z80/mocap_hardware/cad_drawings/hand/imu_holder_middle.stl

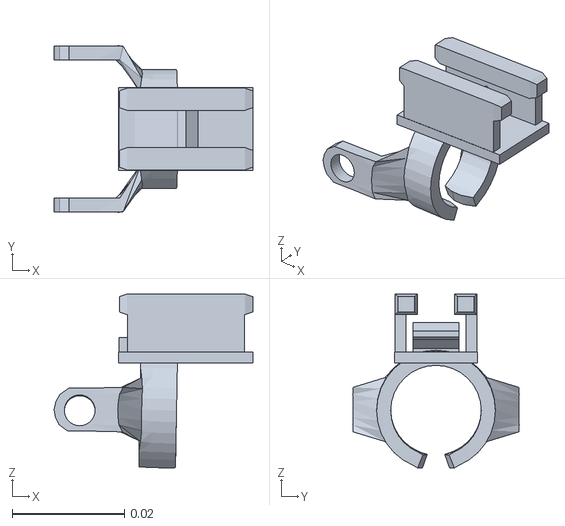
[picture p16: CAD file, 2025-03-31]
cad_drawings/hand/imu_holder_middle.stl
0.0354 x 0.0296 x 0.0309
