z80/mocap_hardware/cad_drawings/hand/imu_holder_pointing.stl

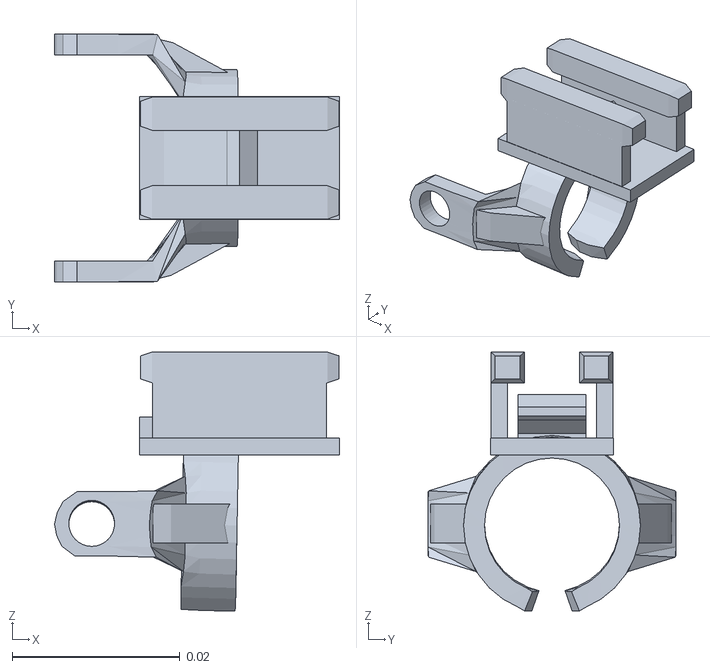
[picture p17: CAD file, 2025-03-31]
cad_drawings/hand/imu_holder_pointing.stl
0.034 x 0.0296 x 0.0309
