z80/mocap_hardware/cad_drawings/hand/pointing_a.stl

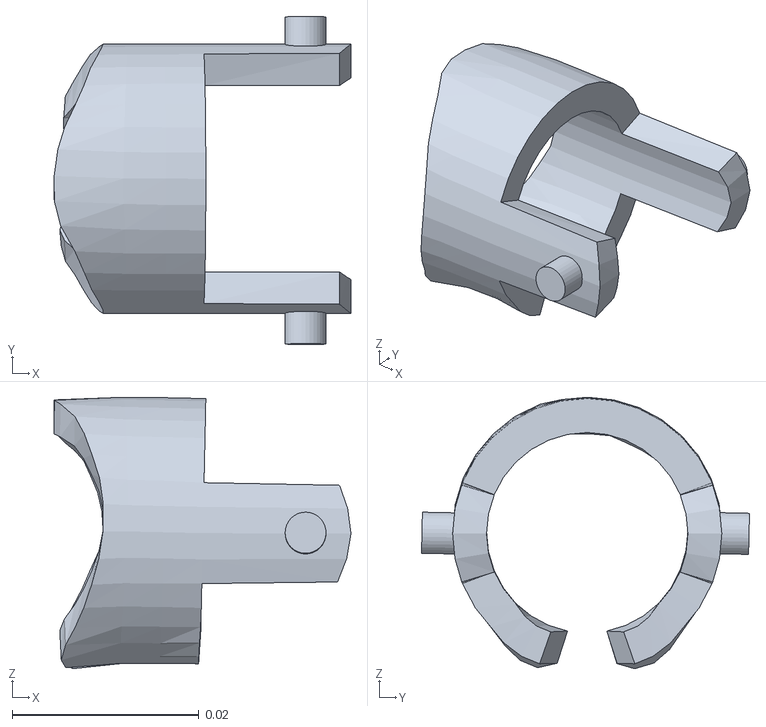
[picture p18: CAD file, 2025-03-31]
cad_drawings/hand/pointing_a.stl
0.0318 x 0.0352 x 0.0291
