z80/mocap_hardware/cad_drawings/hand/palm_b.stl

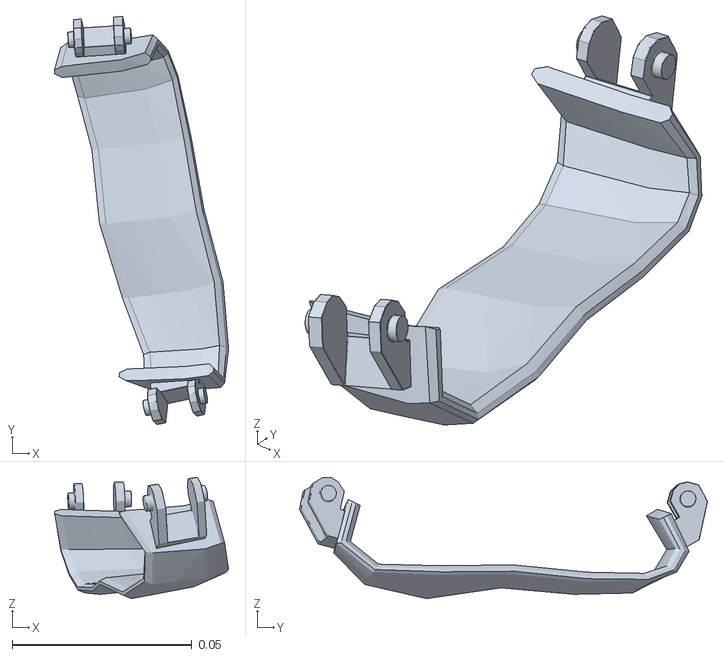
[picture p19: CAD file, 2025-03-31]
cad_drawings/hand/palm_b.stl
0.0485 x 0.113 x 0.0337
