z80/mocap_hardware/cad_drawings/hand/hand_b.stl

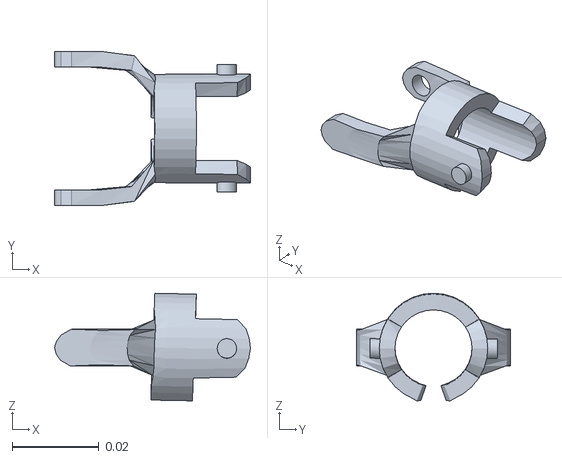
[picture p20: CAD file, 2025-03-31]
cad_drawings/hand/hand_b.stl
0.0452 x 0.0356 x 0.0248
