z80/mocap_hardware/cad_drawings/hand/pinky_b.stl

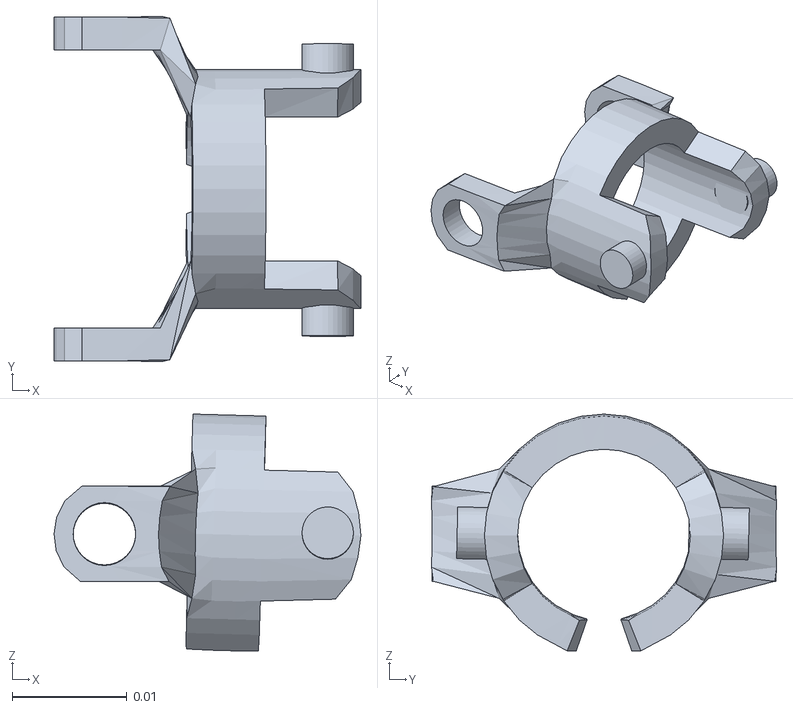
[picture p21: CAD file, 2025-03-31]
cad_drawings/hand/pinky_b.stl
0.0267 x 0.03 x 0.0206
