z80/mocap_hardware/cad_drawings/hand/palm_a.stl

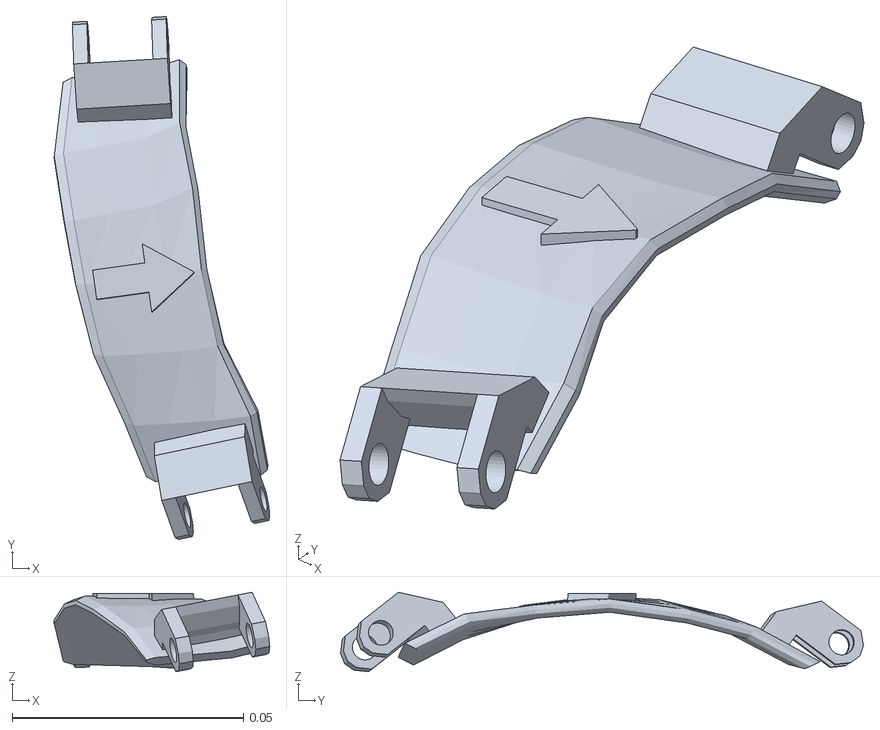
[picture p22: CAD file, 2025-03-31]
cad_drawings/hand/palm_a.stl
0.0466 x 0.113 x 0.0172
