z80/mocap_hardware/cad_drawings/hand/pinky_a.stl

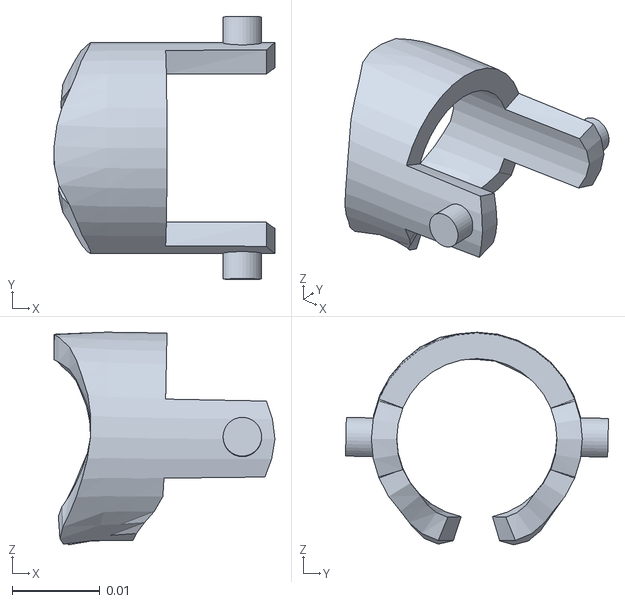
[picture p23: CAD file, 2025-03-31]
cad_drawings/hand/pinky_a.stl
0.0252 x 0.03 x 0.0242
