z80/mocap_hardware/cad_drawings/hand/imu_holder_palm_l.stl

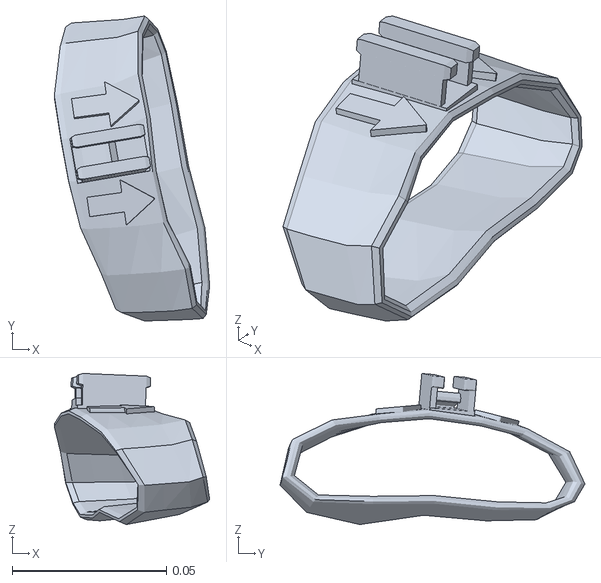
[picture p24: CAD file, 2025-03-31]
cad_drawings/hand/imu_holder_palm_l.stl
0.0504 x 0.0988 x 0.049
