z80/mocap_hardware/cad_drawings/hand/pinky_c.stl

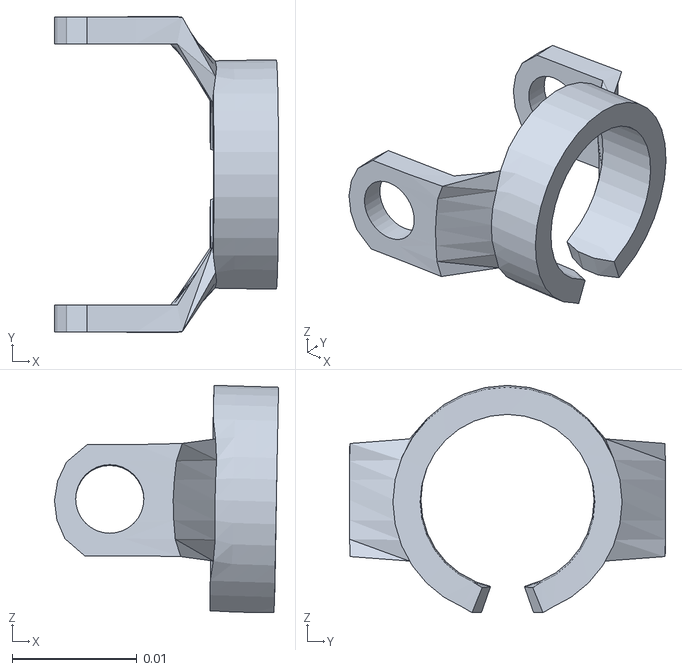
[picture p25: CAD file, 2025-03-31]
cad_drawings/hand/pinky_c.stl
0.018 x 0.0253 x 0.0182
