z80/mocap_hardware/cad_drawings/hand/imu_holder_pinky.stl

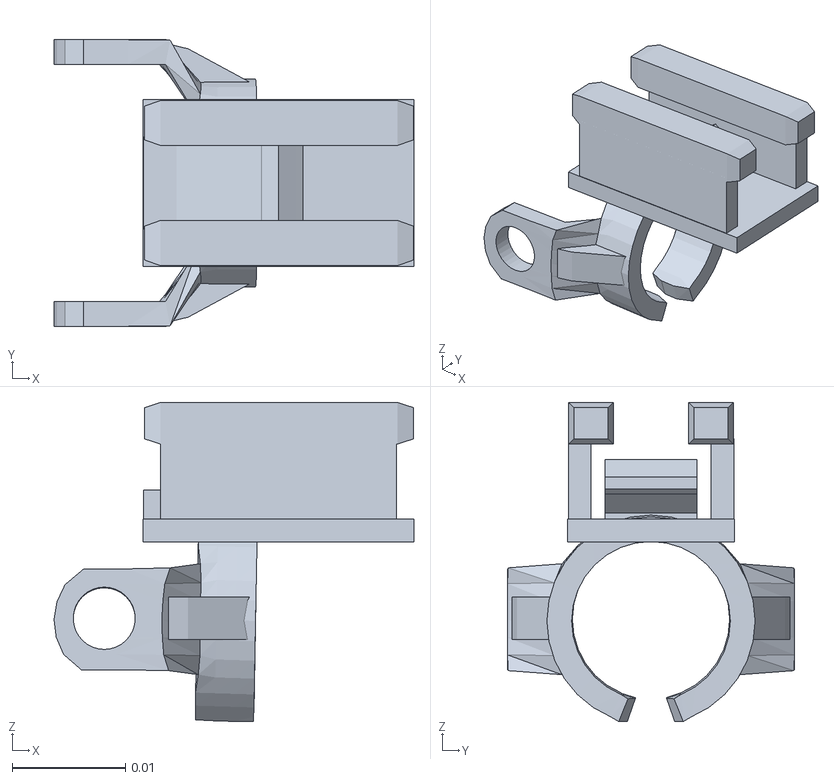
[picture p26: CAD file, 2025-03-31]
cad_drawings/hand/imu_holder_pinky.stl
0.0318 x 0.0253 x 0.0281
