z80/mocap_hardware/cad_drawings/hand/imu_holder_palm_r.stl

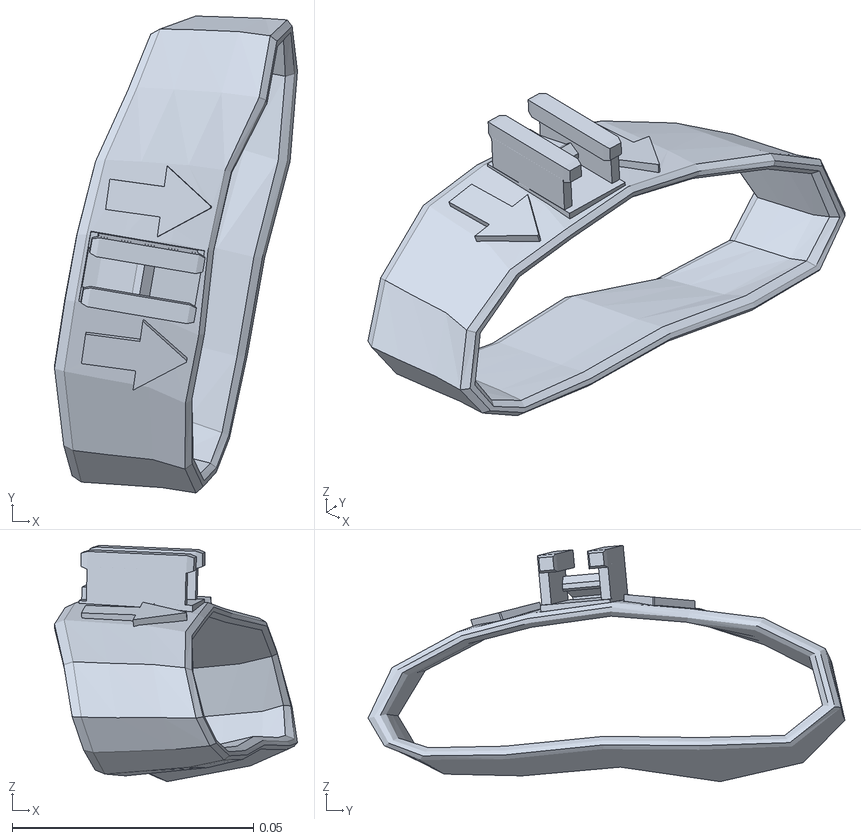
[picture p27: CAD file, 2025-03-31]
cad_drawings/hand/imu_holder_palm_r.stl
0.0504 x 0.0988 x 0.049
