z80/mocap_hardware/cad_drawings/hand/pointing_b.stl

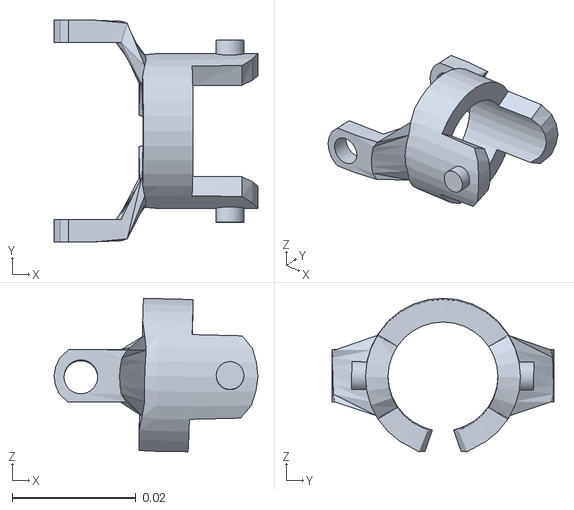
[picture p28: CAD file, 2025-03-31]
cad_drawings/hand/pointing_b.stl
0.033 x 0.0358 x 0.0248
