z80/mocap_hardware/cad_drawings/hand/thumb_b.stl

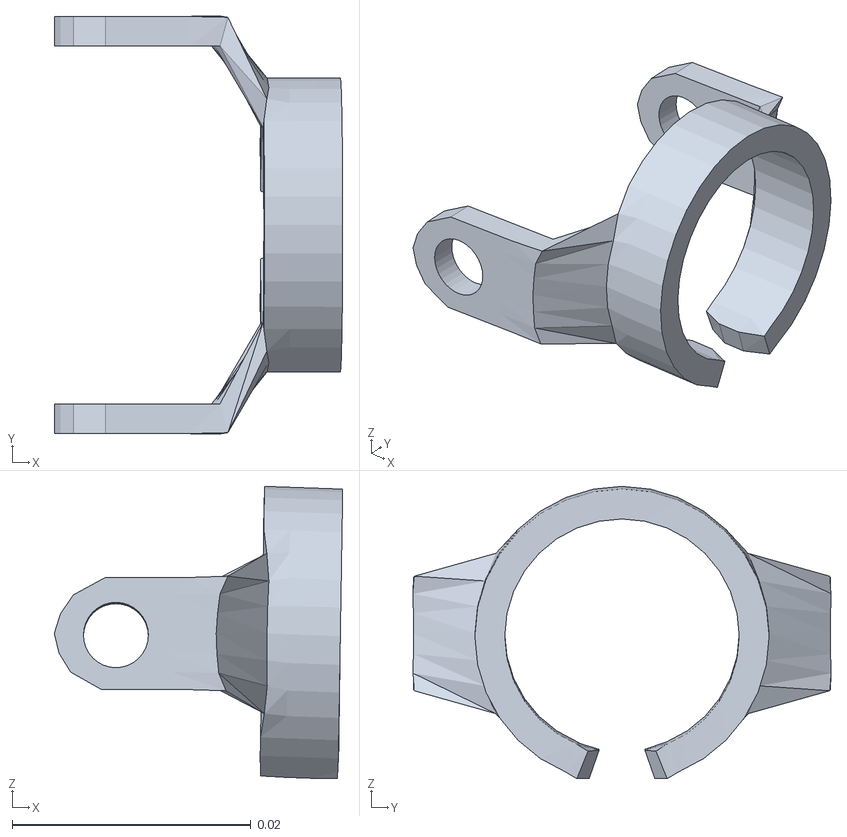
[picture p29: CAD file, 2025-03-31]
cad_drawings/hand/thumb_b.stl
0.0242 x 0.035 x 0.0245
