z80/mocap_hardware/stm32_cube_workspace/stm32_cube_project/stm32_cube_project.ioc

Mcu.UserName=STM32F405RGTx
PA0-WKUP.Signal=ADCx_IN0
PA10.Signal=USART1_RX
PA13.Signal=SYS_JTMS-SWDIO
PA14.Signal=SYS_JTCK-SWCLK
PA15.GPIO_Label=PARALLEL_LOAD
PA15.Signal=GPIO_Output
PA2.Signal=USART2_TX
PA3.Signal=USART2_RX
PA5.GPIO_Label=LED_0
PA5.Signal=GPIO_Output
PA6.GPIO_Label=LED_1
PA6.Signal=GPIO_Output
PA7.GPIO_Label=LED_2
PA7.Signal=GPIO_Output
PA9.Signal=USART1_TX
PB10.Signal=I2C2_SCL
PB11.Signal=I2C2_SDA
PB14.Signal=USB_OTG_HS_DM
PB15.Signal=USB_OTG_HS_DP
PB6.Signal=I2C1_SCL
PB7.Signal=I2C1_SDA
PC10.GPIO_Label=DATA_SERIAL
PC10.Signal=GPIO_Input
PC11.GPIO_Label=SHIFTER_CLOCK
PC11.Signal=GPIO_Output
PH0-OSC_IN.Signal=RCC_OSC_IN
PH1-OSC_OUT.Signal=RCC_OSC_OUT
