z80/mocap_hardware/stm32_cube_workspace/stm32_cube_project/Core/Inc/main.h

#define LED_0_Pin GPIO_PIN_5
#define LED_0_GPIO_Port GPIOA
#define LED_1_Pin GPIO_PIN_6
#define LED_1_GPIO_Port GPIOA
#define LED_2_Pin GPIO_PIN_7
#define LED_2_GPIO_Port GPIOA
#define PARALLEL_LOAD_Pin GPIO_PIN_15
#define PARALLEL_LOAD_GPIO_Port GPIOA
#define DATA_SERIAL_Pin GPIO_PIN_10
#define DATA_SERIAL_GPIO_Port GPIOC
#define SHIFTER_CLOCK_Pin GPIO_PIN_11
#define SHIFTER_CLOCK_GPIO_Port GPIOC
