z80/mocap_hardware/stm32_cube_workspace/stm32_cube_project/Src/task_led.h

#ifndef __TASK_LED_H_
#define __TASK_LED_H_

#include "main.h"

void task_led_init();

void set_leds( uint8_t led );
void set_led( uint8_t index, uint8_t en );
void set_instant_leds( uint8_t led );
void set_instant_led( uint8_t index, uint8_t en );


#endif
