z80/mocap_hardware/stm32_cube_workspace/stm32_cube_project/Src/bmi085_io.h

#ifndef __BMI085_IO_H_
#define __BMI085_IO_H_

#include "main.h"

uint8_t bmi085_init( uint8_t index );

uint8_t bmi085_switch_irq( uint8_t index );

uint8_t bmi085_read_acc_irq( uint8_t index, uint8_t * data );
uint8_t bmi085_read_gyro_irq( uint8_t index, uint8_t * data );



#endif
